TDA-2030/Holocube/firmware/main/HoloCubic_AIO/Image/6397732914.jpg

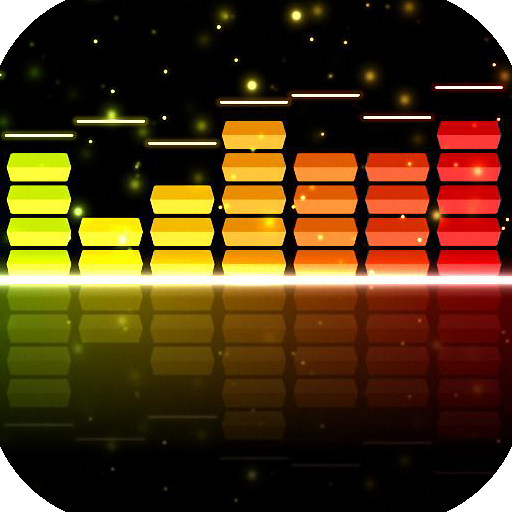
firmware/main/HoloCubic_AIO/Image/6397732914.jpg
