TDA-2030/Holocube/firmware/main/HoloCubic_AIO/Image/app_2048.jpg

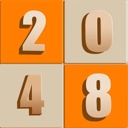
firmware/main/HoloCubic_AIO/Image/app_2048.jpg
