TDA-2030/Holocube/firmware/main/HoloCubic_AIO/Image/app_bilibili.png

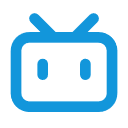
firmware/main/HoloCubic_AIO/Image/app_bilibili.png
