TDA-2030/Holocube/firmware/main/HoloCubic_AIO/Image/app_file_manager.png

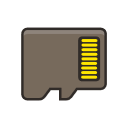
firmware/main/HoloCubic_AIO/Image/app_file_manager.png
