TDA-2030/Holocube/firmware/main/HoloCubic_AIO/Image/app_file_maneger_1.png

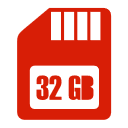
firmware/main/HoloCubic_AIO/Image/app_file_maneger_1.png
