TDA-2030/Holocube/firmware/main/HoloCubic_AIO/Image/app_movie2.png

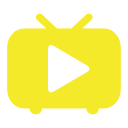
firmware/main/HoloCubic_AIO/Image/app_movie2.png
