TDA-2030/Holocube/firmware/main/HoloCubic_AIO/Image/app_screen.png

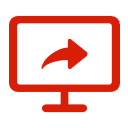
firmware/main/HoloCubic_AIO/Image/app_screen.png
