TDA-2030/Holocube/firmware/main/HoloCubic_AIO/Image/bilibili.png

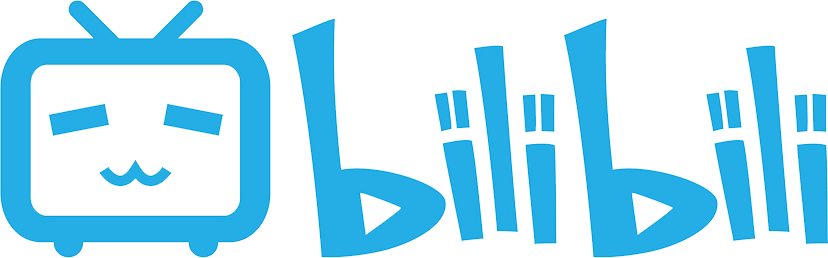
firmware/main/HoloCubic_AIO/Image/bilibili.png
