TDA-2030/Holocube/firmware/main/HoloCubic_AIO/Image/butterfly_1.jpg

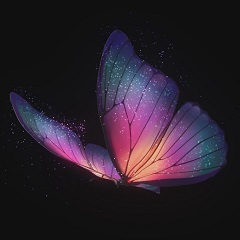
firmware/main/HoloCubic_AIO/Image/butterfly_1.jpg
