TDA-2030/Holocube/firmware/main/HoloCubic_AIO/Image/butterfly_2.jpg

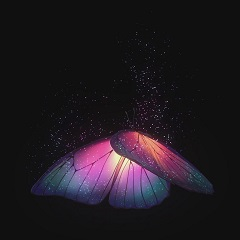
firmware/main/HoloCubic_AIO/Image/butterfly_2.jpg
