TDA-2030/Holocube/firmware/main/HoloCubic_AIO/Image/holocubic_1080x1080.jpg

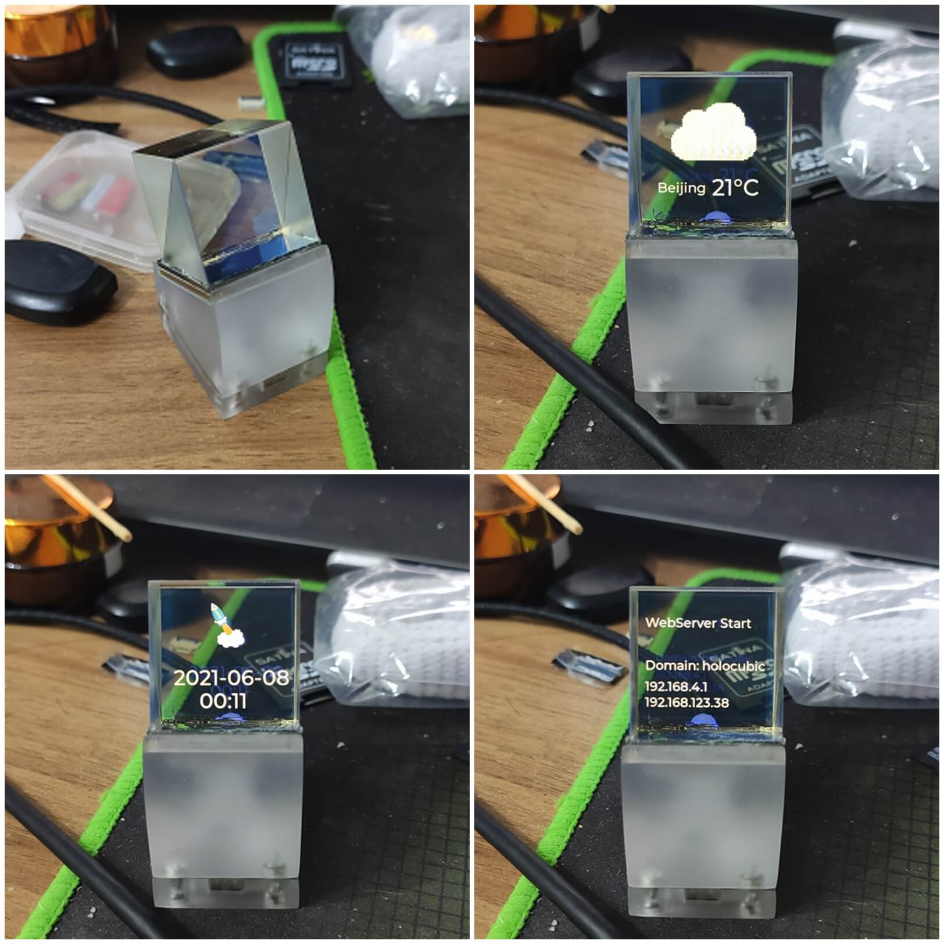
firmware/main/HoloCubic_AIO/Image/holocubic_1080x1080.jpg
