TDA-2030/Holocube/firmware/main/HoloCubic_AIO/Image/holocubic_AIO_Frame.png

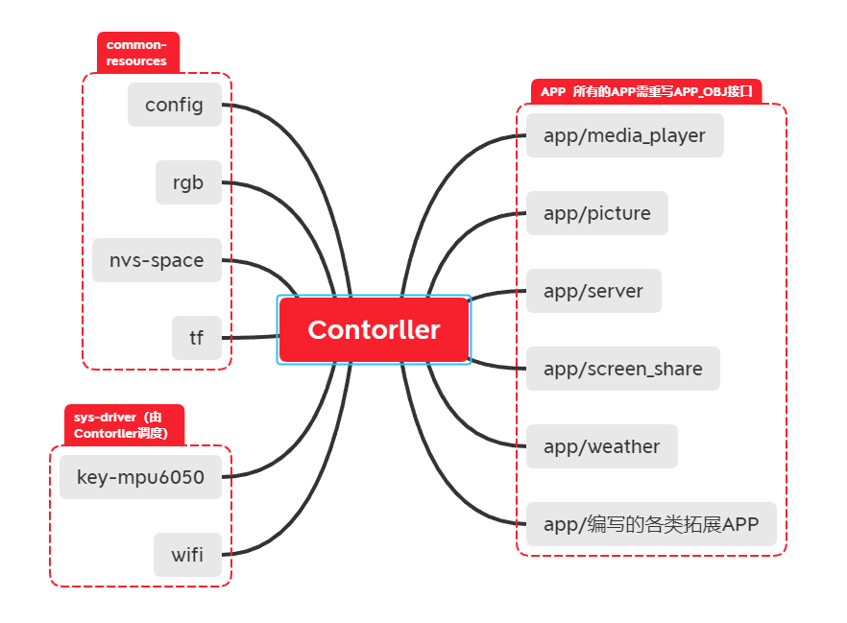
firmware/main/HoloCubic_AIO/Image/holocubic_AIO_Frame.png
