TDA-2030/Holocube/firmware/main/HoloCubic_AIO/Image/holocubic_aio_tool.png

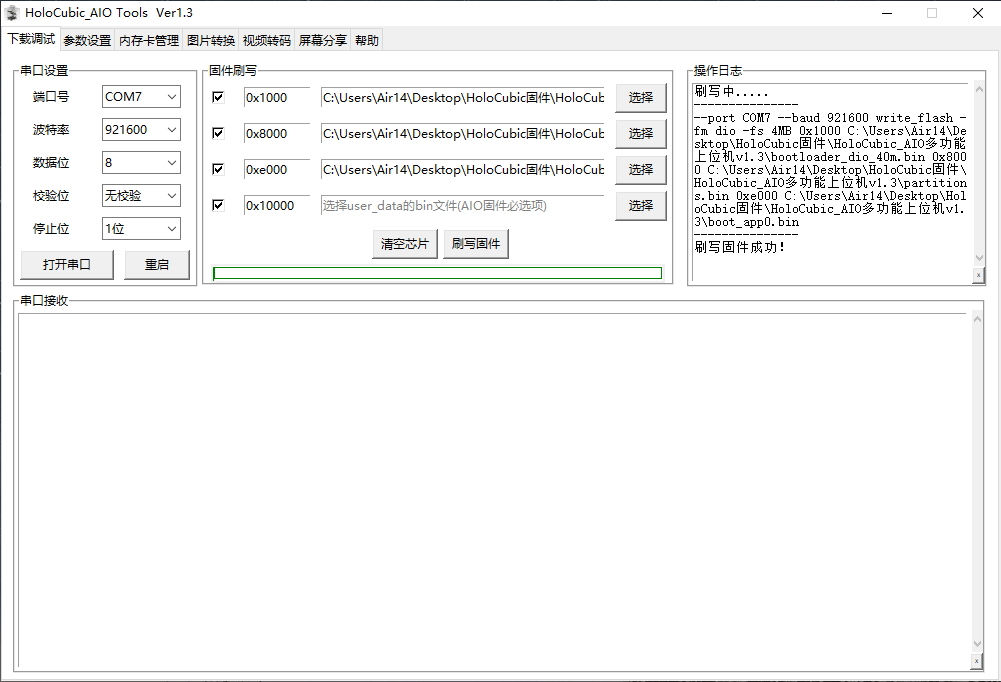
firmware/main/HoloCubic_AIO/Image/holocubic_aio_tool.png
