TDA-2030/Holocube/firmware/main/HoloCubic_AIO/Image/holocubic_extern_err.png

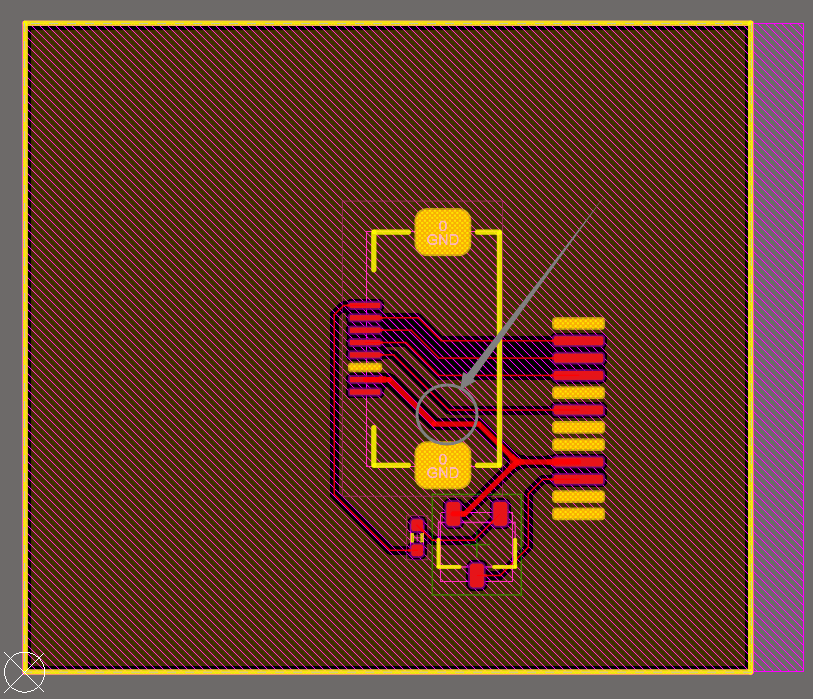
firmware/main/HoloCubic_AIO/Image/holocubic_extern_err.png
