TDA-2030/Holocube/firmware/main/HoloCubic_AIO/Image/holocubic_main.jpg

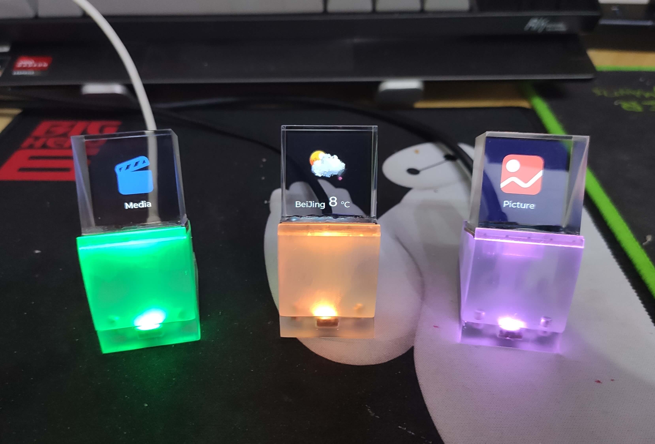
firmware/main/HoloCubic_AIO/Image/holocubic_main.jpg
