TDA-2030/Holocube/firmware/main/HoloCubic_AIO/Image/holocubic_qq_group.jpg

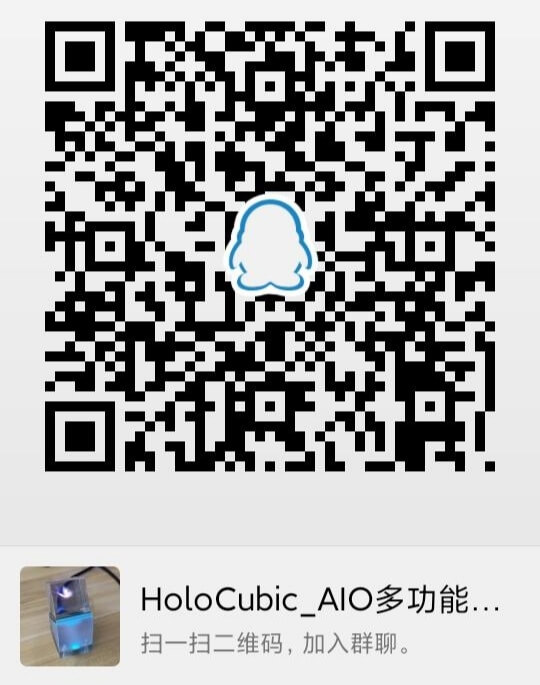
firmware/main/HoloCubic_AIO/Image/holocubic_qq_group.jpg
