TDA-2030/Holocube/firmware/main/HoloCubic_AIO/Image/holocubic_scr_compare.jpg

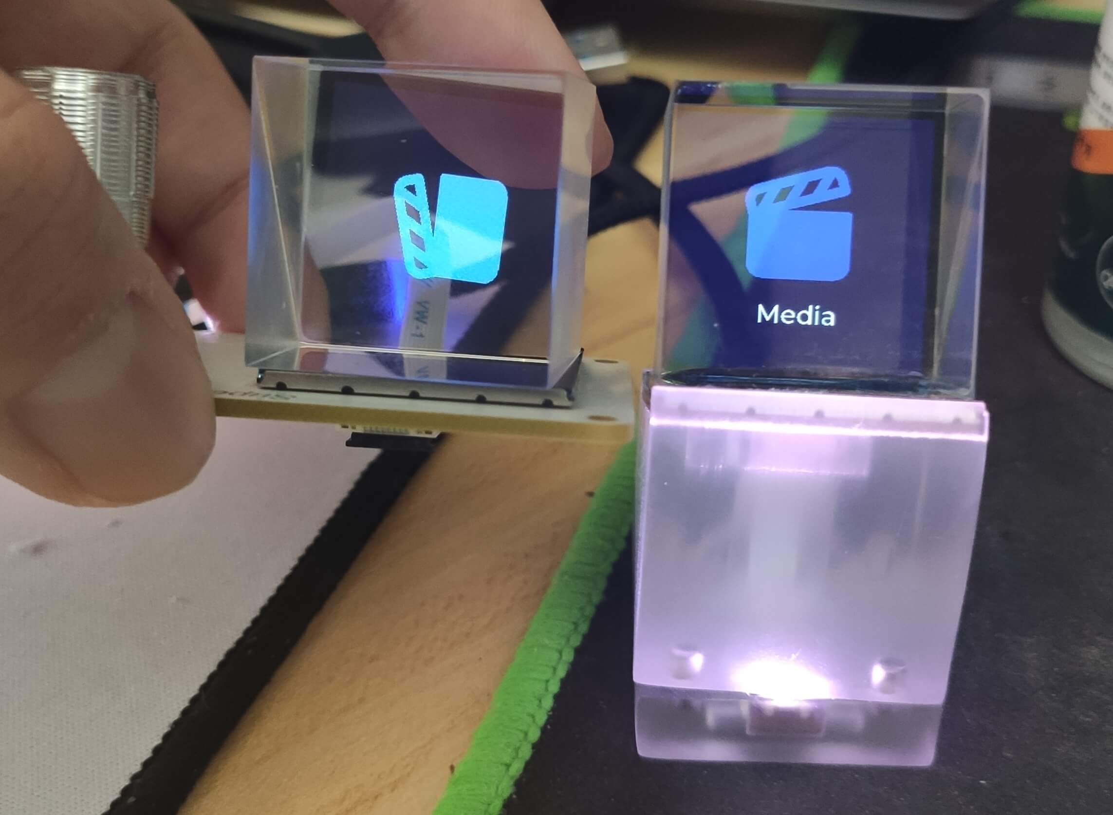
firmware/main/HoloCubic_AIO/Image/holocubic_scr_compare.jpg
