TDA-2030/Holocube/firmware/main/HoloCubic_AIO/Image/holocubic_setting.png

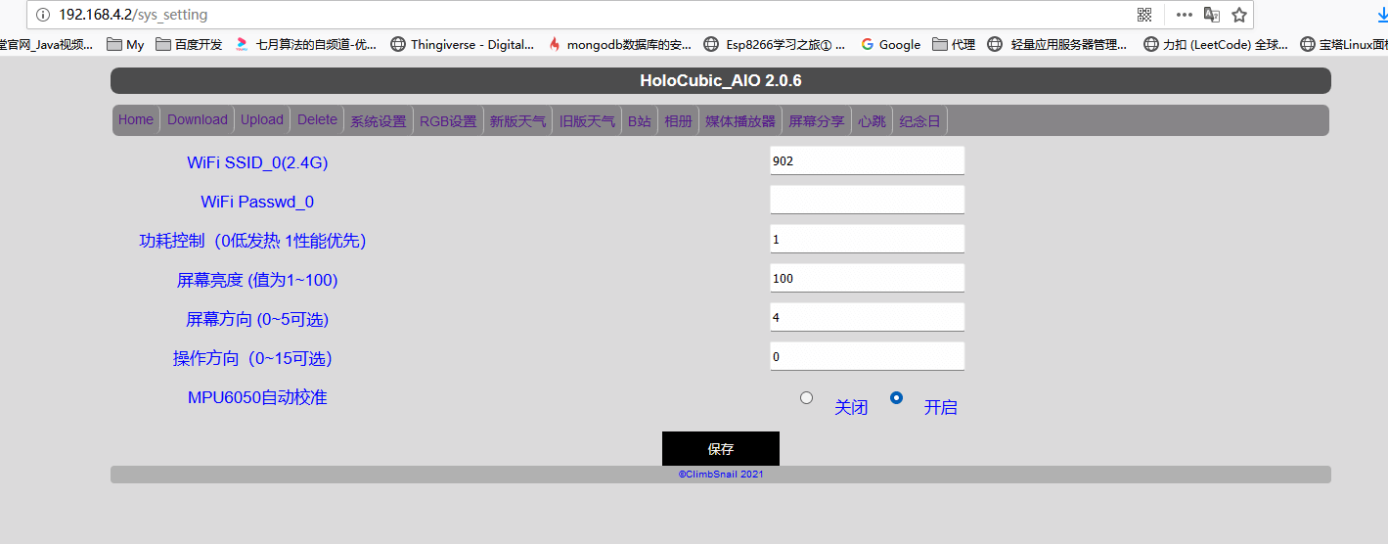
firmware/main/HoloCubic_AIO/Image/holocubic_setting.png
