TDA-2030/Holocube/firmware/main/HoloCubic_AIO/Image/holocubic_upload.png

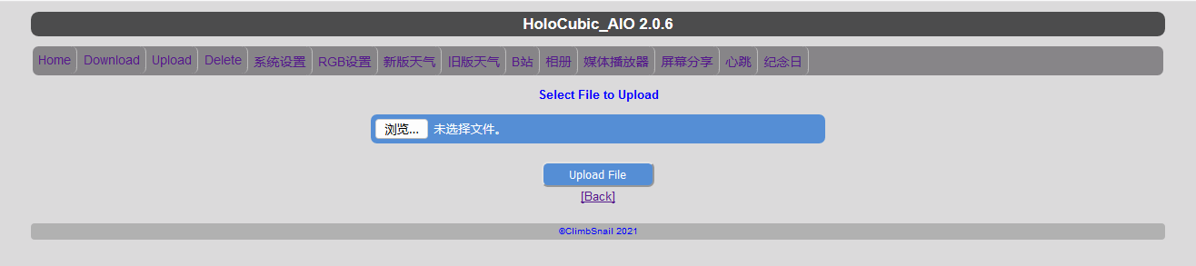
firmware/main/HoloCubic_AIO/Image/holocubic_upload.png
