TDA-2030/Holocube/firmware/main/HoloCubic_AIO/Image/settings.png

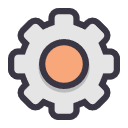
firmware/main/HoloCubic_AIO/Image/settings.png
