TDA-2030/Holocube/firmware/main/HoloCubic_AIO/Image/settings_1.png

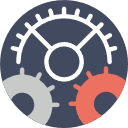
firmware/main/HoloCubic_AIO/Image/settings_1.png
