TDA-2030/Holocube/firmware/main/HoloCubic_AIO/Image/thought_anim_2.png

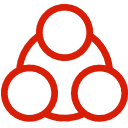
firmware/main/HoloCubic_AIO/Image/thought_anim_2.png
