TDA-2030/Holocube/hardware/main_board/image/holocubic_back.png

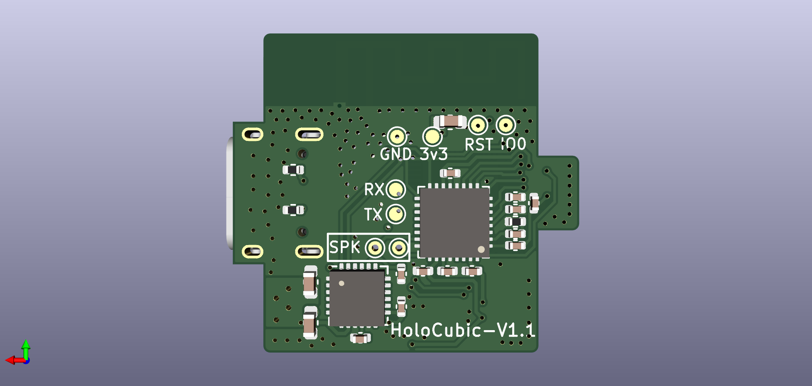
hardware/main_board/image/holocubic_back.png
