TDA-2030/Holocube/hardware/screen_sub_board/image/screen_sub_board.png

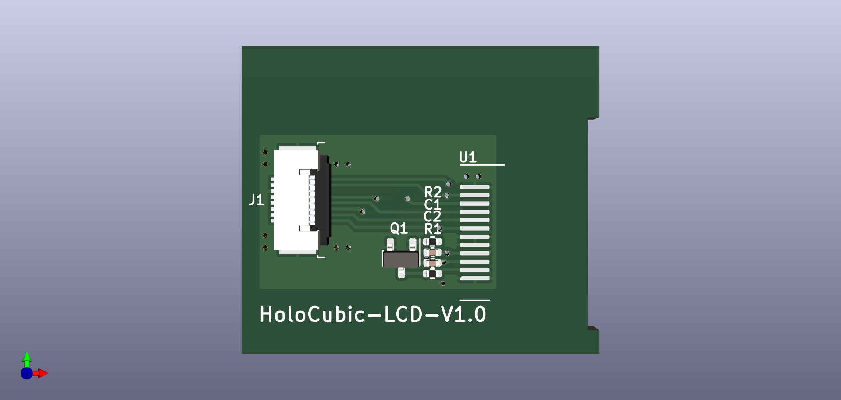
hardware/screen_sub_board/image/screen_sub_board.png
