TDA-2030/Holocube/firmware/components/lvgl/src/lv_examples/src/lv_ex_style/lv_ex_style_1.png

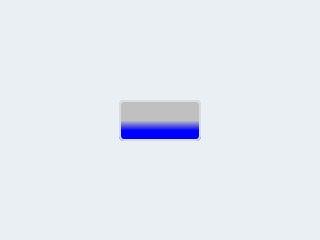
firmware/components/lvgl/src/lv_examples/src/lv_ex_style/lv_ex_style_1.png
