TDA-2030/Holocube/firmware/components/lvgl/src/lv_examples/src/lv_ex_widgets/lv_ex_gauge/lv_ex_gauge_2.png

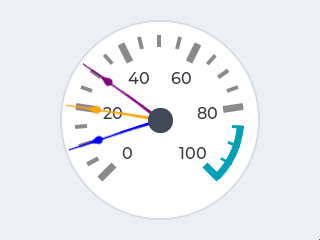
firmware/components/lvgl/src/lv_examples/src/lv_ex_widgets/lv_ex_gauge/lv_ex_gauge_2.png
