TDA-2030/Holocube/firmware/components/lvgl/src/lv_examples/src/lv_ex_widgets/lv_ex_textarea/lv_ex_textarea_3.png

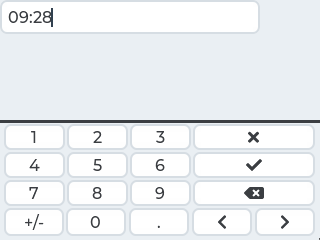
firmware/components/lvgl/src/lv_examples/src/lv_ex_widgets/lv_ex_textarea/lv_ex_textarea_3.png
