TDA-2030/Holocube/firmware/components/webpage_config/html/wifi.png

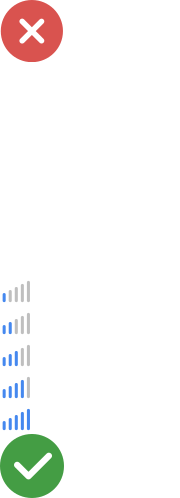
firmware/components/webpage_config/html/wifi.png
