TDA-2030/Holocube/firmware/components/libjpeg/jpeg-9a/testimg.bmp

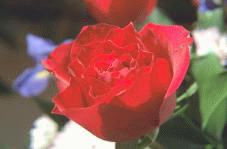
firmware/components/libjpeg/jpeg-9a/testimg.bmp
