TDA-2030/Holocube/firmware/main/HoloCubic_AIO/HoloCubic_Firmware/src/driver/disk_fs.cpp

#include <string.h>
#include "disk_fs.h"


static void join_path(char *dst_path, const char *pre_path, const char *rear_path)
{
    while (*pre_path != 0) {
        *dst_path = *pre_path;
        ++dst_path;
        ++pre_path;
    }
    if (*(pre_path - 1) != '/') {
        *dst_path = '/';
        ++dst_path;
    }

    if (*rear_path == '/') {
        ++rear_path;
    }
    while (*rear_path != 0) {
        *dst_path = *rear_path;
        ++dst_path;
        ++rear_path;
    }
    *dst_path = 0;
}

Disk_FS::Disk_FS(fs::FS &fs): m_fs(fs)
{

}

Disk_FS::~Disk_FS()
{

}

const char *Disk_FS::get_file_basename(const char *path)
{
    // 获取最后一个'/'所在的下标
    const char *ret = path;
    for (const char *cur = path; *cur != 0; ++cur) {
        if (*cur == '/') {
            ret = cur + 1;
        }
    }
    return ret;
}

void Disk_FS::listDir(const char *dirname, uint8_t levels)
{
    Serial.printf("Listing directory: %s\n", dirname);
    photo_file_num = 0;

    File root = m_fs.open(dirname);
    if (!root) {
        Serial.println("Failed to open directory");
        return;
    }
    if (!root.isDirectory()) {
        Serial.println("Not a directory");
        return;
    }

    int dir_len = strlen(dirname) + 1;

    File file = root.openNextFile();
    while (file && photo_file_num < DIR_FILE_NUM) {
        if (file.isDirectory()) {
            Serial.print("  DIR : ");
            Serial.println(file.name());
            if (levels) {
                listDir(file.name(), levels - 1);
            }
        } else {
            Serial.print("  FILE: ");
            // 只取文件名 保存到file_name_list中
            strncpy(file_name_list[photo_file_num], file.name() + dir_len, DIR_FILE_NAME_MAX_LEN - 1);
            file_name_list[photo_file_num][strlen(file_name_list[photo_file_num]) - 4] = 0;

            char file_name[FILENAME_MAX_LEN] = {0};
            sprintf(file_name, "%s/%s.bin", dirname, file_name_list[photo_file_num]);
            Serial.print(file_name);
            ++photo_file_num;
            Serial.print("  SIZE: ");
            Serial.println(file.size());
        }
        file = root.openNextFile();
    }
    Serial.println(photo_file_num);
}

File_Info *Disk_FS::listDir(const char *dirname)
{
    Serial.printf("Listing directory: %s\n", dirname);

    File root = m_fs.open(dirname);
    if (!root) {
        Serial.println("Failed to open directory");
        return NULL;
    }
    if (!root.isDirectory()) {
        Serial.println("Not a directory");
        return NULL;
    }

    int dir_len = strlen(dirname) + 1;

    // 头节点的创建（头节点用来记录此文件夹）
    File_Info *head_file = (File_Info *)malloc(sizeof(File_Info));
    head_file->file_type = FILE_TYPE_FOLDER;
    head_file->file_name = (char *)malloc(dir_len);
    // 将文件夹名赋值给头节点（当作这个节点的文件名）
    strncpy(head_file->file_name, dirname, dir_len - 1);
    head_file->file_name[dir_len - 1] = 0;
    head_file->front_node = NULL;
    head_file->next_node = NULL;

    File_Info *file_node = head_file;

    File file = root.openNextFile();
    while (file) {
        // if (levels)
        // {
        //     listDir(file.name(), levels - 1);
        // }
        const char *fn = get_file_basename(file.name());
        // 字符数组长度为实际字符串长度+1
        int filename_len = strlen(fn);
        if (filename_len > FILENAME_MAX_LEN - 10) {
            Serial.println("Filename is too long.");
        }

        // 创建新节点
        file_node->next_node = (File_Info *)malloc(sizeof(File_Info));
        // 让下一个节点指向当前节点
        // （此时第一个节点的front_next会指向head节点，等遍历结束再调一下）
        file_node->next_node->front_node = file_node;
        // file_node指针移向节点
        file_node = file_node->next_node;

        // 船家创建新节点的文件名
        file_node->file_name = (char *)malloc(filename_len);
        strncpy(file_node->file_name, fn, filename_len); //
        file_node->file_name[filename_len] = 0;          //
        // 下一个节点赋空
        file_node->next_node = NULL;

        char tmp_file_name[FILENAME_MAX_LEN] = {0};
        // sprintf(tmp_file_name, "%s/%s", dirname, file_node->file_name);
        join_path(tmp_file_name, dirname, file_node->file_name);
        if (file.isDirectory()) {
            file_node->file_type = FILE_TYPE_FOLDER;
            // 类型为文件夹
            Serial.print("  DIR : ");
            Serial.println(tmp_file_name);
        } else {
            file_node->file_type = FILE_TYPE_FILE;
            // 类型为文件
            Serial.print("  FILE: ");
            Serial.print(tmp_file_name);
            Serial.print("  SIZE: ");
            Serial.println(file.size());
        }

        file = root.openNextFile();
    }

    if (NULL != head_file->next_node) {
        // 将最后一个节点的next_node指针指向 head_file->next_node
        file_node->next_node = head_file->next_node;
        // 调整第一个数据节点的front_node指针（非head节点）
        head_file->next_node->front_node = file_node;
    }
    return head_file;
}

void Disk_FS::release_file_info(File_Info *info)
{
    File_Info *cur_node = NULL; // 记录当前节点
    if (NULL == info) {
        return;
    }
    for (cur_node = info->next_node; NULL != cur_node;) {
        // 判断是不是循环一圈回来了
        if (info->next_node == cur_node) {
            break;
        }
        File_Info *tmp = cur_node; // 保存准备删除的节点
        cur_node = cur_node->next_node;
        free(tmp);
    }
    free(info);
}

void Disk_FS::createDir(const char *path)
{
    Serial.printf("Creating Dir: %s\n", path);
    if (m_fs.mkdir(path)) {
        Serial.println("Dir created");
    } else {
        Serial.println("mkdir failed");
    }
}

void Disk_FS::removeDir(const char *path)
{
    Serial.printf("Removing Dir: %s\n", path);
    if (m_fs.rmdir(path)) {
        Serial.println("Dir removed");
    } else {
        Serial.println("rmdir failed");
    }
}

void Disk_FS::readFile(const char *path)
{
    Serial.printf("Reading file: %s\n", path);

    File file = m_fs.open(path);
    if (!file) {
        Serial.println("Failed to open file for reading");
        return;
    }

    Serial.print("Read from file: ");
    while (file.available()) {
        Serial.write(file.read());
    }
    file.close();
}

uint16_t Disk_FS::readFile(const char *path, uint8_t *info)
{
    Serial.printf("Reading file: %s\r\n", path);

    File file = m_fs.open(path);
    uint16_t ret_len = 0;
    if (!file || file.isDirectory()) {
        Serial.println("- failed to open file for reading");
        return ret_len;
    }

    // Serial.println("- read from file:");
    while (file.available()) {
        ret_len += file.read(info + ret_len, 15);
        // Serial.write(file.read());
    }
    file.close();
    return ret_len;
}

String Disk_FS::readFileLine(const char *path, int num)
{
    Serial.printf("Reading file: %s line: %d\n", path, num);

    File file = m_fs.open(path);
    if (!file) {
        return ("Failed to open file for reading");
    }

    char *p = buf;
    while (file.available()) {
        char c = file.read();
        if (c == '\n') {
            num--;
            if (num == 0) {
                *(p++) = '\0';
                String s(buf);
                s.trim();
                return s;
            }
        } else if (num == 1) {
            *(p++) = c;
        }
    }
    file.close();

    return String("error parameter!");
}

void Disk_FS::writeFile(const char *path, const char *info)
{
    Serial.printf("Writing file: %s\n", path);

    File file = m_fs.open(path, FILE_WRITE);
    if (!file) {
        Serial.println("Failed to open file for writing");
        return;
    }
    if (file.println(info)) {
        Serial.println("Write succ");
    } else {
        Serial.println("Write failed");
    }
    file.close();
}

File Disk_FS::open(const String &path, const char *mode)
{
    return m_fs.open(path, FILE_WRITE);
}

void Disk_FS::appendFile(const char *path, const char *message)
{
    Serial.printf("Appending to file: %s\n", path);

    File file = m_fs.open(path, FILE_APPEND);
    if (!file) {
        Serial.println("Failed to open file for appending");
        return;
    }
    if (file.print(message)) {
        Serial.println("Message appended");
    } else {
        Serial.println("Append failed");
    }
    file.close();
}

void Disk_FS::renameFile(const char *path1, const char *path2)
{
    Serial.printf("Renaming file %s to %s\n", path1, path2);
    if (m_fs.rename(path1, path2)) {
        Serial.println("File renamed");
    } else {
        Serial.println("Rename failed");
    }
}

boolean Disk_FS::deleteFile(const char *path)
{
    Serial.printf("Deleting file: %s\n", path);
    if (m_fs.remove(path)) {
        Serial.println("File deleted");
        return true;
    } else {
        Serial.println("Delete failed");
    }
    return false;
}

boolean Disk_FS::deleteFile(const String &path)
{
    Serial.printf("Deleting file: %s\n", path);
    if (m_fs.remove(path)) {
        Serial.println("File deleted");
        return true;
    } else {
        Serial.println("Delete failed");
    }
    return false;
}

void Disk_FS::readBinFromSd(const char *path, uint8_t *buf)
{
    File file = m_fs.open(path);
    size_t len = 0;
    if (file) {
        len = file.size();

        while (len) {
            size_t toRead = len;
            if (toRead > 512) {
                toRead = 512;
            }
            file.read(buf, toRead);
            len -= toRead;
        }

        file.close();
    } else {
        Serial.println("Failed to open file for reading");
    }
}

void Disk_FS::writeBinToSd(const char *path, uint8_t *buf)
{
    File file = m_fs.open(path, FILE_WRITE);
    if (!file) {
        Serial.println("Failed to open file for writing");
        return;
    }

    size_t i;
    for (i = 0; i < 2048; i++) {
        file.write(buf, 512);
    }
    file.close();
}

void Disk_FS::fileIO(const char *path)
{
    File file = m_fs.open(path);
    static uint8_t buf[512];
    size_t len = 0;
    uint32_t start = millis();
    uint32_t end = start;
    if (file) {
        len = file.size();
        size_t flen = len;
        start = millis();
        while (len) {
            size_t toRead = len;
            if (toRead > 512) {
                toRead = 512;
            }
            file.read(buf, toRead);
            len -= toRead;
        }
        end = millis() - start;
        Serial.printf("%u bytes read for %u ms\n", flen, end);
        file.close();
    } else {
        Serial.println("Failed to open file for reading");
    }

    file = m_fs.open(path, FILE_WRITE);
    if (!file) {
        Serial.println("Failed to open file for writing");
        return;
    }

    size_t i;
    start = millis();
    for (i = 0; i < 2048; i++) {
        file.write(buf, 512);
    }
    end = millis() - start;
    Serial.printf("%u bytes written for %u ms\n", 2048 * 512, end);
    file.close();
}
