TDA-2030/Holocube/firmware/main/app_sr_handler.c

/*
 * SPDX-FileCopyrightText: 2015-2022 Espressif Systems (Shanghai) CO LTD
 *
 * SPDX-License-Identifier: Unlicense OR CC0-1.0
 */

#include <string.h>
#include "freertos/FreeRTOS.h"
#include "freertos/queue.h"
#include "esp_heap_caps.h"
#include "esp_log.h"
#include "esp_check.h"
#include "app_sr.h"
#include "driver/i2s.h"

#include "app_sr_handler.h"
#include "settings.h"


static const char *TAG = "sr_handler";

static bool b_audio_playing = false;

typedef enum {
    AUDIO_WAKE,
    AUDIO_OK,
    AUDIO_END,
    AUDIO_MAX,
} audio_segment_t;

typedef struct {
    uint8_t *audio_buffer;
    size_t len;
} audio_data_t;

static audio_data_t g_audio_data[AUDIO_MAX];

static esp_err_t sr_echo_play(audio_segment_t audio)
{

    typedef struct {
        // The "RIFF" chunk descriptor
        uint8_t ChunkID[4];
        int32_t ChunkSize;
        uint8_t Format[4];
        // The "fmt" sub-chunk
        uint8_t Subchunk1ID[4];
        int32_t Subchunk1Size;
        int16_t AudioFormat;
        int16_t NumChannels;
        int32_t SampleRate;
        int32_t ByteRate;
        int16_t BlockAlign;
        int16_t BitsPerSample;
        // The "data" sub-chunk
        uint8_t Subchunk2ID[4];
        int32_t Subchunk2Size;
    } wav_header_t;

    /**
     * read head of WAV file
     */
    uint8_t *p = g_audio_data[audio].audio_buffer;
    wav_header_t *wav_head = (wav_header_t *)p;
    if (NULL == strstr((char *)wav_head->Subchunk1ID, "fmt") &&
            NULL == strstr((char *)wav_head->Subchunk2ID, "data")) {
        ESP_LOGE(TAG, "Header of wav format error");
        return ESP_FAIL;
    }
    p += sizeof(wav_header_t);
    size_t len = g_audio_data[audio].len - sizeof(wav_header_t);
    len = len & 0xfffffffc;
    ESP_LOGD(TAG, "frame_rate=%d, ch=%d, width=%d", wav_head->SampleRate, wav_head->NumChannels, wav_head->BitsPerSample);

    i2s_zero_dma_buffer(I2S_NUM_0);
    vTaskDelay(pdMS_TO_TICKS(50));
    size_t bytes_written = 0;
    b_audio_playing = true;
    i2s_write(I2S_NUM_0, p, len, &bytes_written, portMAX_DELAY);
    i2s_zero_dma_buffer(I2S_NUM_0);
    vTaskDelay(pdMS_TO_TICKS(20));
    b_audio_playing = false;
    return ESP_OK;
}

bool sr_echo_is_playing(void)
{
    return b_audio_playing;
}

void sr_handler_task(void *pvParam)
{
    esp_err_t ret;
    FILE *fp;
    const sys_param_t *param = settings_get_parameter();
    const char *files[2][3] = {
        {"/spiffs/echo_en_wake.wav", "/spiffs/echo_en_ok.wav", "/spiffs/echo_en_end.wav"},
        {"/spiffs/echo_cn_wake.wav", "/spiffs/echo_cn_ok.wav", "/spiffs/echo_cn_end.wav"},
    };
    // char audio_file[48] = {0};
    // for (size_t i = 0; i < AUDIO_MAX; i++) {
    //     strncpy(audio_file, files[param->sr_lang][i], sizeof(audio_file));
    //     fp = fopen(audio_file, "rb");
    //     ESP_GOTO_ON_FALSE(NULL != fp, ESP_ERR_NOT_FOUND, err, TAG, "Open file %s failed", audio_file);
    //     size_t file_size = fm_get_file_size(audio_file);
    //     g_audio_data[i].len = file_size;
    //     g_audio_data[i].audio_buffer = heap_caps_calloc(1, file_size, MALLOC_CAP_8BIT | MALLOC_CAP_SPIRAM);
    //     ESP_GOTO_ON_FALSE(NULL != g_audio_data[i].audio_buffer, ESP_ERR_NO_MEM, err, TAG,  "No mem for sr echo buffer");
    //     fread(g_audio_data[i].audio_buffer, 1, file_size, fp);
    //     fclose(fp);
    // }
    (void)ret;

    while (true) {
        sr_result_t result;
        app_sr_get_result(&result, portMAX_DELAY);
        // char audio_file[48] = {0};

    }

    goto err;

err:
    if (fp) {
        fclose(fp);
    }
    vTaskDelete(NULL);
}
