TDA-2030/Holocube/firmware/main/HoloCubic_AIO/HoloCubic_Firmware/src/app_sntp.h

/*
  * ESPRESSIF MIT License
  *
  * Copyright (c) 2017 <ESPRESSIF SYSTEMS (SHANGHAI) PTE LTD>
  *
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
  */
#ifndef _APP_SNTP_H_
#define _APP_SNTP_H_

#include <sys/time.h>

#ifdef __cplusplus
extern "C" {
#endif

void app_sntp_init(void);


#ifdef __cplusplus
}
#endif

#endif
