TDA-2030/Holocube/firmware/main/HoloCubic_AIO/HoloCubic_Firmware/src/driver/codec.h

/*
 * SPDX-FileCopyrightText: 2015-2022 Espressif Systems (Shanghai) CO LTD
 *
 * SPDX-License-Identifier: Apache-2.0
 */

#ifndef __CODEC_H__
#define __CODEC_H__


#ifdef __cplusplus
extern "C" {
#endif

void codec_init(void);
void codec_deinit(void);

#ifdef __cplusplus
}
#endif

#endif
