TDA-2030/Holocube/firmware/main/HoloCubic_AIO/HoloCubic_Firmware/src/app/anniversary/anniversary_gui.h

#ifndef APP_ANNIVERSARY_GUI_H
#define APP_ANNIVERSARY_GUI_H

#include "time.h"
#include "lvgl.h"

#ifdef __cplusplus
extern "C"
{
#endif

#define ANIEND                      \
    while (lv_anim_count_running()) \
        lv_task_handler(); //等待动画完成

void anniversary_gui_init(void);
void display_anniversary(const char *file_name, lv_scr_load_anim_t anim_type, struct tm *target_date, int anniversary_day_count, const char *event_name);
void anniversary_gui_display_date(struct tm *target, int anniversary_day_count, const char *event_name);
void anniversary_gui_set_txtlabel(char *txt);
void anniversary_gui_del(void);
void anniversary_obj_del(void);


#ifdef __cplusplus
} /* extern "C" */
#endif

#endif
