TDA-2030/Holocube/firmware/main/HoloCubic_AIO/HoloCubic_Firmware/src/app/bilibili_fans/bilibili_gui.h

#ifndef APP_BILIBILI_GUI_H
#define APP_BILIBILI_GUI_H

#include "lvgl.h"

#ifdef __cplusplus
extern "C"
{
#endif

#define ANIEND                      \
    while (lv_anim_count_running()) \
        lv_task_handler(); //等待动画完成

void bilibili_gui_init(void);
void display_bilibili(const char *file_name, lv_scr_load_anim_t anim_type, const char *, const char * );
void bilibili_obj_del(void);
void bilibili_gui_del(void);


#ifdef __cplusplus
} /* extern "C" */
#endif

#endif
